Acmex2564/Z31-DigiDash/Images/ex_IMG_20210104_2118395.jpg

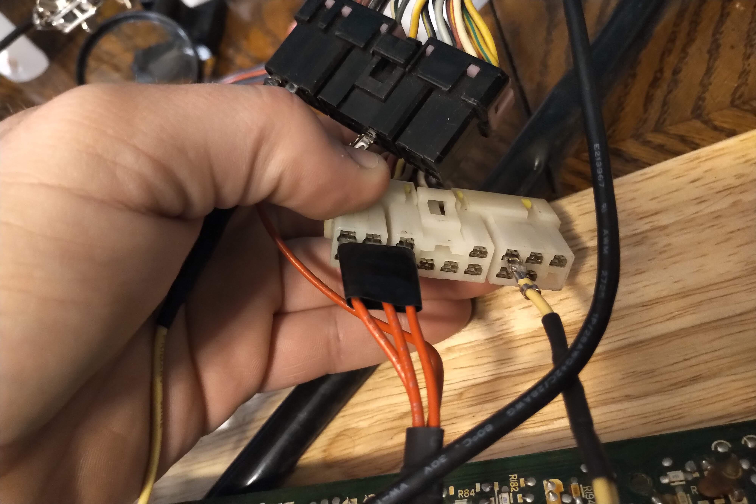
Images/ex_IMG_20210104_2118395.jpg
