Acmex2564/Z31-DigiDash/Images/Waveform_FD_Fuel_1.PNG

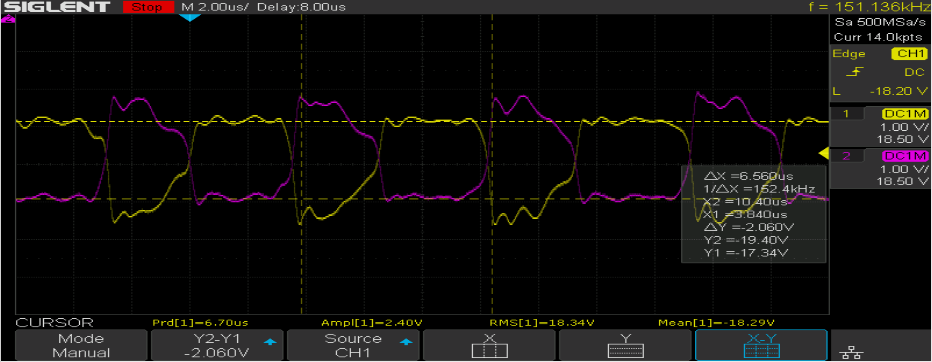
Images/Waveform_FD_Fuel_1.PNG
