Acmex2564/Z31-DigiDash/Images/Waveform_FD_RHS.PNG

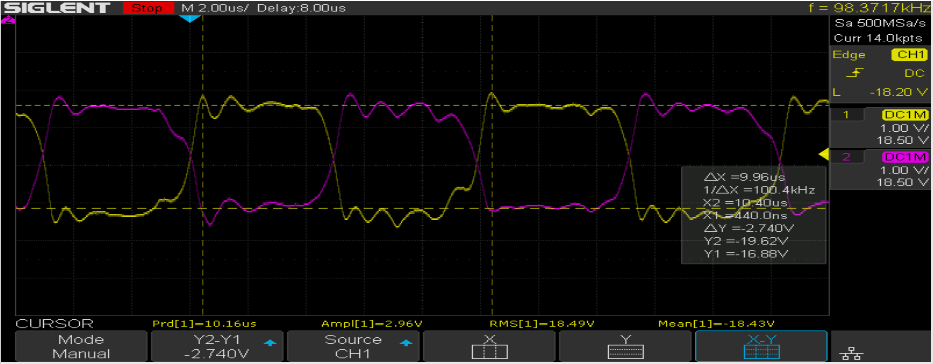
Images/Waveform_FD_RHS.PNG
