Acmex2564/Z31-DigiDash/Images/Waveform_FD_Tach.PNG

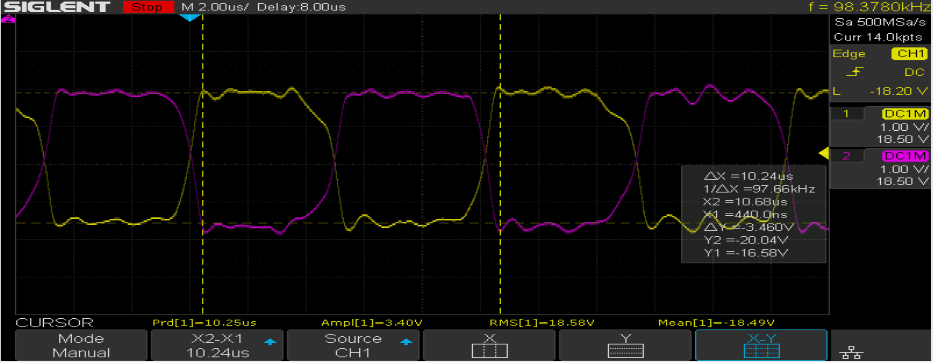
Images/Waveform_FD_Tach.PNG
